grafmar/scope-footswitch-trigger/src/pc_app/scopes/lecroy.py

from .base import BaseScope
import pyvisa
from PIL import Image
import io


# ----------------------------
# LeCroy Scope
# ----------------------------
class LeCroyScope(BaseScope):

    def identify(self, enable: bool):
        if enable:
            self.scope.write('MESSAGE "FOOT SWITCH IDENTIFIER"')
        else:
            self.scope.write('MESSAGE ""')

    def run(self):
        self.scope.write("TRIG_MODE NORM")
        self.running = True

    def stop(self):
        self.scope.write("TRIG_MODE STOP")
        self.running = False

    def single(self):
        self.scope.write("TRIG_MODE SINGLE")

    def trigger_auto(self):
        self.scope.write("TRIG_MODE AUTO")

    def trigger_force(self):
        self.scope.write("TRIG_MODE AUTO")
        self.scope.write("WAIT")
        self.scope.write("TRIG_MODE STOP")

    def trigger_normal(self):
        self.scope.write("TRIG_MODE NORM")

    def get_screenshot_png(self, color: bool, inverted: bool) -> bytes:
        bckg = "WHITE" if inverted else "BLACK"

        # configure hardcopy for screenshot (TIFF, GPIB port, background color)
        self.scope.write(f"HCSU DEV,TIFF,PORT,GPIB,BCKG,{bckg}")

        # trigger screenshot
        data = self.scope.query_binary_values(
            "SCDP",
            datatype='B',
            container=bytes
        )

        # convert TIFF -> PNG
        image = Image.open(io.BytesIO(data))
        png_buffer = io.BytesIO()
        image.save(png_buffer, format="PNG")

        return png_buffer.getvalue()

    def get_setup(self) -> bytes:

        # --- Binary mode ---
        self.scope.write_termination = ''
        self.scope.read_termination = ''
        old_timeout = self.scope.timeout
        self.scope.timeout = 5000

        # --- Request setup ---
        raw = self.scope.query_binary_values( # SAVE/RECALL SETUP PANEL_SETUP, PNSU
            "PNSU?",
            datatype='B',
            container=bytes
        )

        # --- Restore ASCII mode ---
        self.scope.write_termination = '\n'
        self.scope.read_termination = '\n'
        self.scope.timeout = old_timeout

        return raw

    def write_setup_data(self, data: bytes) -> bool:
        try:
            self.scope.write_termination = ''
            self.scope.read_termination = ''

            # Send direct to device without any processing, as the setup file is already in the correct binary format
            self.scope.write_raw(data)
            self.scope.flush(pyvisa.constants.VI_WRITE_BUF)

            self.scope.write_termination = '\n'
            self.scope.read_termination = '\n'

            return True

        except Exception as e:
            self.log(f"Setup write error: {e}")
            return False
